vagarthgaurav/MIDI-visualizer/schematic-design/MIDI Visualiser.kicad_sch

## KiCad design schematic-design/MIDI Visualiser.kicad_sch (2023-10-24)

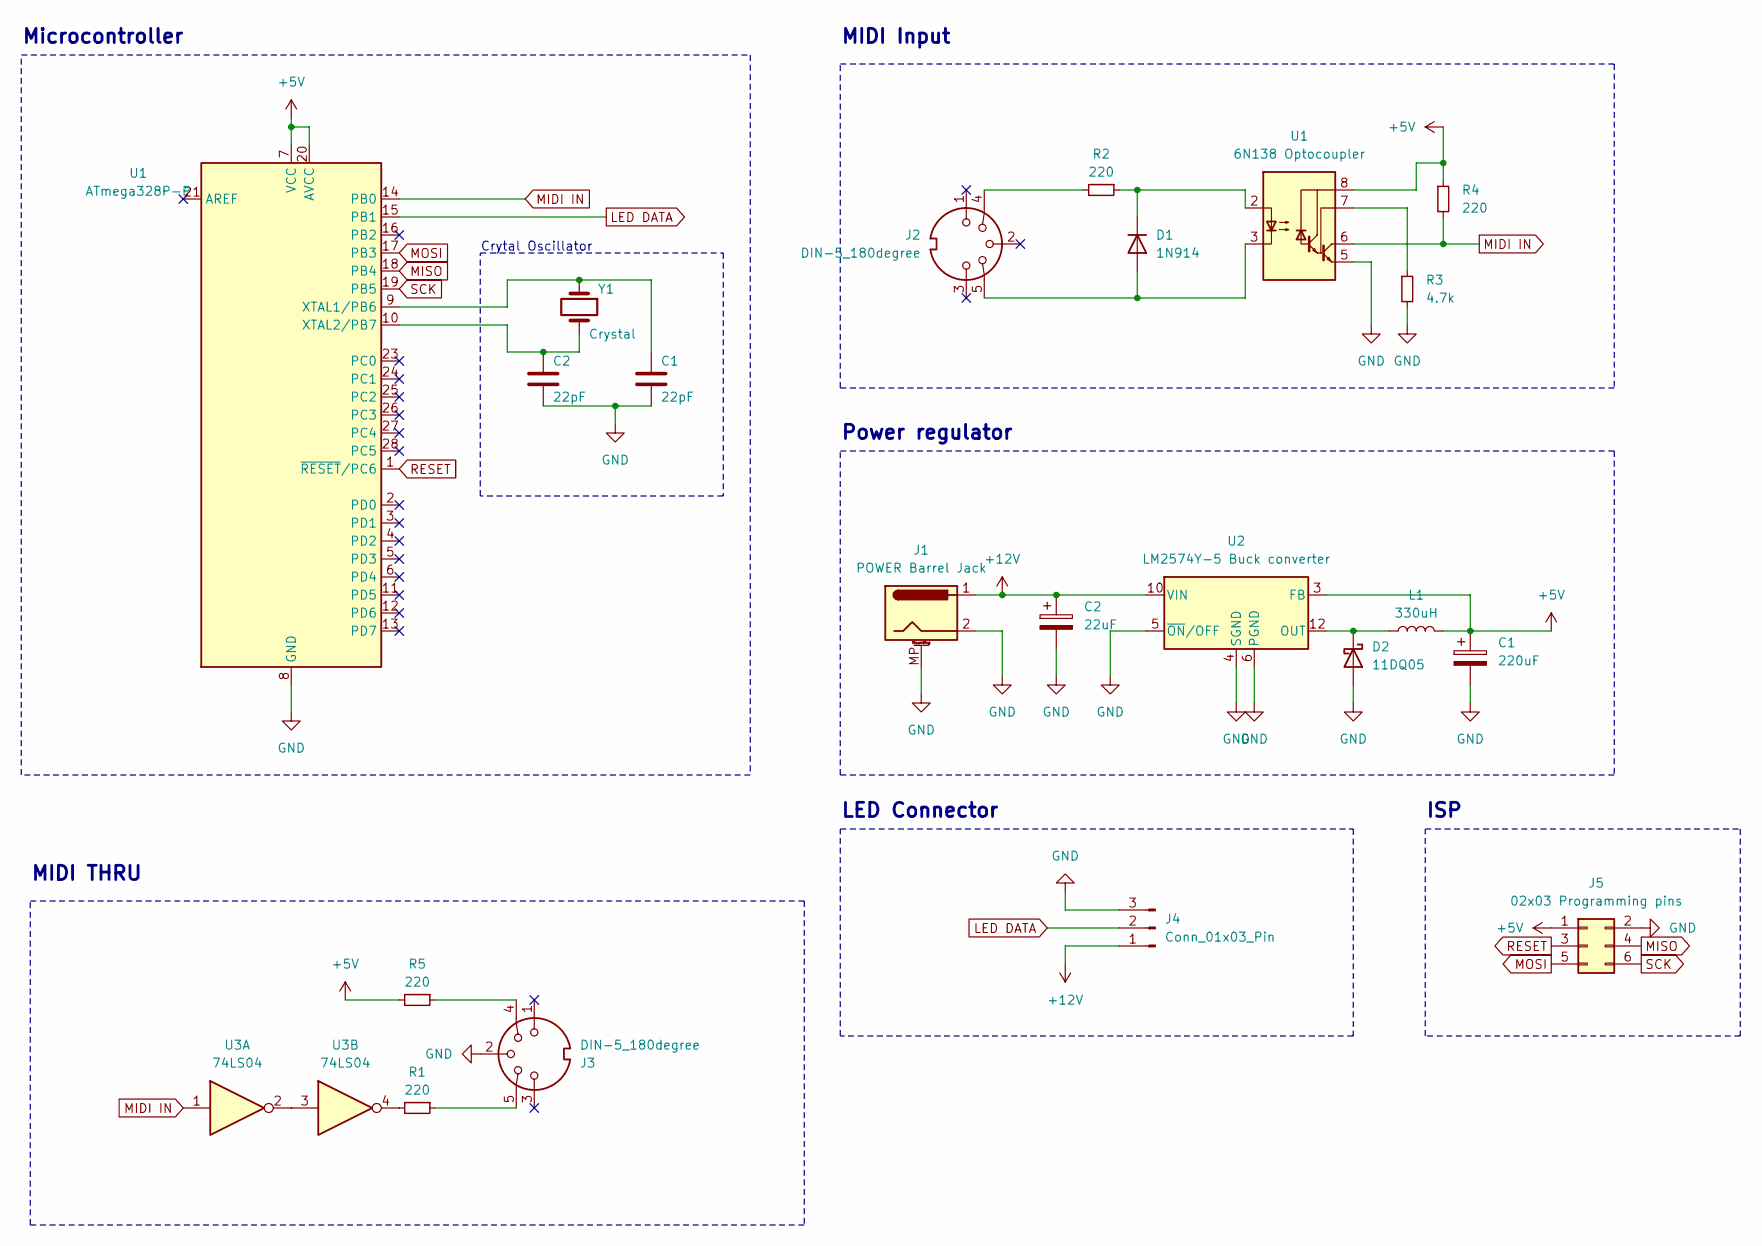
[picture p17: schematic MIDI Visualiser.kicad_sch]

Parts:
C1: 220uF
C2: 22uF
D1: 1N914; D_DO-35_SOD27_P7.62mm_Horizontal
D2: 11DQ05
J1: POWER Barrel Jack
J2, J3: DIN-5_180degree
J4: Conn_01x03_Pin
J5: 02x03 Programming pins
L1: 330uH
R1, R2, R4, R5: 220
R3: 4.7k
U1: 6N138 Optocoupler
U2: LM2574Y-5 Buck converter; SOIC-14W_7.5x9mm_P1.27mm
U3: 74LS04
Y1: Crystal

Connections:
+5V: C1.1, J5.1, L1.2, R4.1, R5.2, U1.7 (VCC), U1.8 (GND), U1.20 (AVCC), U2.3 (FB)
+12V: C2.1, J1.1, J4.1, U2.10 (VIN)
GND: C1.1, C1.2, C2.2, D2.2 (A), J1.2, J1.MP (MountPin), J3.2, J4.3, J5.2, R3.2, U1.5 (PD3), U1.8 (GND), U1.22 (GND), U2.4 (SGND), U2.5 (~ON/OFF), U2.6 (PGND)
LED DATA: J4.2, U1.15 (PB1)
MIDI IN: R4.2, U1.6 (PD4), U1.14 (PB0), U3.1
MISO: J5.4, U1.18 (PB4)
MOSI: J5.5, U1.17 (PB3)
unnamed: C1.2, U1.9 (XTAL1/PB6), Y1.1
unnamed: C2.1, U1.10 (XTAL2/PB7), Y1.2
unnamed: D1.1 (K), R2.1, U1.2 (PD0)
unnamed: D1.2 (A), J2.5, U1.3 (PD1)
unnamed: D2.1 (K), L1.1, U2.12 (OUT)
unnamed: J2.4, R2.2
unnamed: J3.4, R5.1
unnamed: J3.5, R1.1
unnamed: R1.2, U3.4
unnamed: R3.1, U1.7 (VCC)
unnamed: U3.2, U3.3
RESET: J5.3, U1.1 (~RESET/PC6)
SCK: J5.6, U1.19 (PB5)

Notes on the sheet:
MIDI THRU
Microcontroller
MIDI Input
Crytal Oscillator
LED Connector
Power regulator
ISP
